techlobo/ATX_Switch/Images/ATX_Switch_4_2024-03-25.png

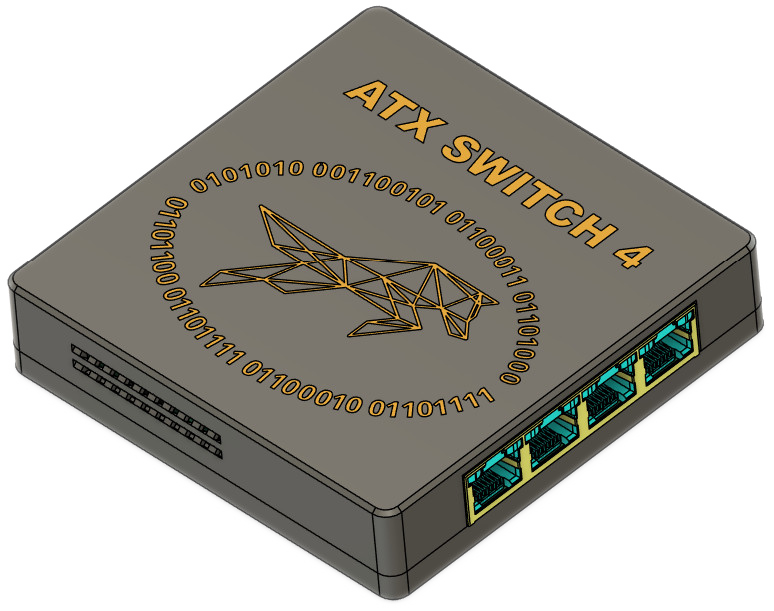
Images/ATX_Switch_4_2024-03-25.png
